AndersonRayner/teensy_4.0_breakout/Software/canTest/canTest/canTest.ino

#include <FlexCAN_T4.h>

FlexCAN_T4<CAN1, RX_SIZE_256, TX_SIZE_16> can1;  // CAN1 : Pin 22, 23
FlexCAN_T4<CAN2, RX_SIZE_256, TX_SIZE_16> can2;  // CAN2 : Pin  0,  1

CAN_message_t msg;

void setup(void) {
  can1.begin();
  can1.setBaudRate(1000000);
  can2.begin();
  can2.setBaudRate(1000000);
}

void loop() {
  

  if ( can1.read(msg) ) {
    Serial.print("CAN1 "); 
    Serial.print("MB: "); Serial.print(msg.mb);
    Serial.print("  ID: 0x"); Serial.print(msg.id, HEX );
    Serial.print("  EXT: "); Serial.print(msg.flags.extended );
    Serial.print("  LEN: "); Serial.print(msg.len);
    Serial.print(" DATA: ");
    for ( uint8_t i = 0; i < 8; i++ ) {
      Serial.print(msg.buf[i]); Serial.print(" ");
    }
    Serial.print("  TS: "); Serial.println(msg.timestamp);
  }
  else if ( can2.read(msg) ) {
    Serial.print("CAN2 "); 
    Serial.print("MB: "); Serial.print(msg.mb);
    Serial.print("  ID: 0x"); Serial.print(msg.id, HEX );
    Serial.print("  EXT: "); Serial.print(msg.flags.extended );
    Serial.print("  LEN: "); Serial.print(msg.len);
    Serial.print(" DATA: ");
    for ( uint8_t i = 0; i < 8; i++ ) {
      Serial.print(msg.buf[i]); Serial.print(" ");
    }
    Serial.print("  TS: "); Serial.println(msg.timestamp);
  }
}
